ikruglov/home-automation/esp32-climarad-v2x/images/pcb-back.png

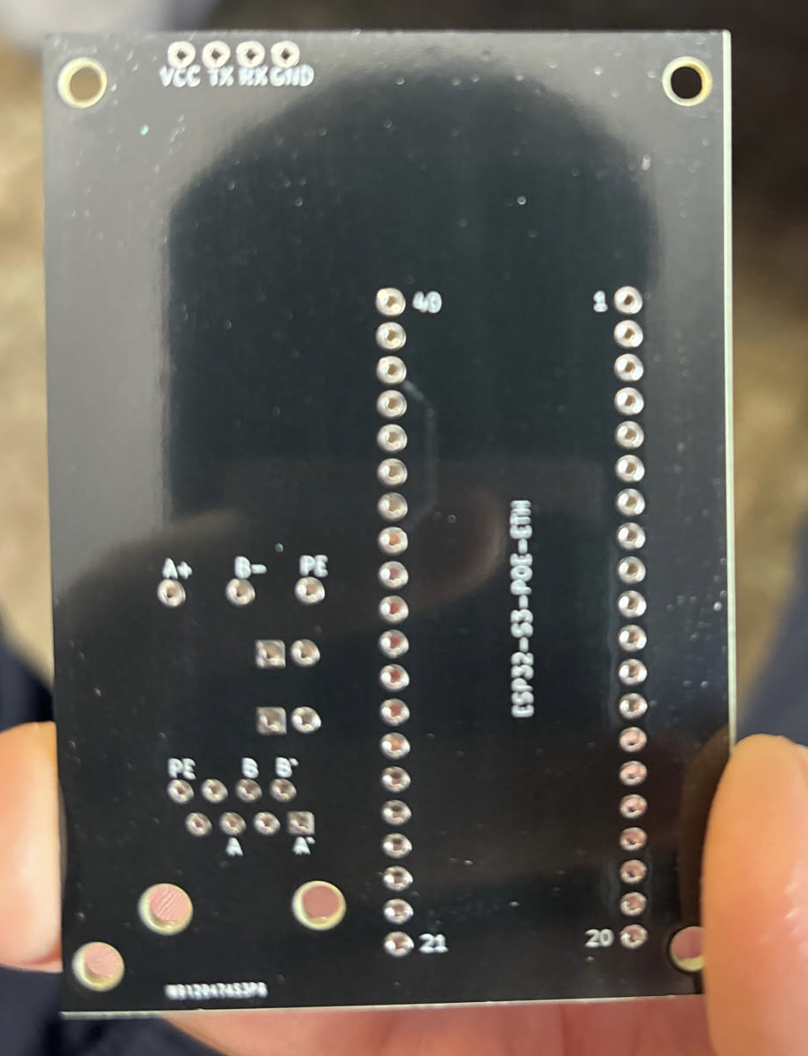
esp32-climarad-v2x/images/pcb-back.png
