ikruglov/home-automation/esp32-climarad-v2x/images/pcb-front.png

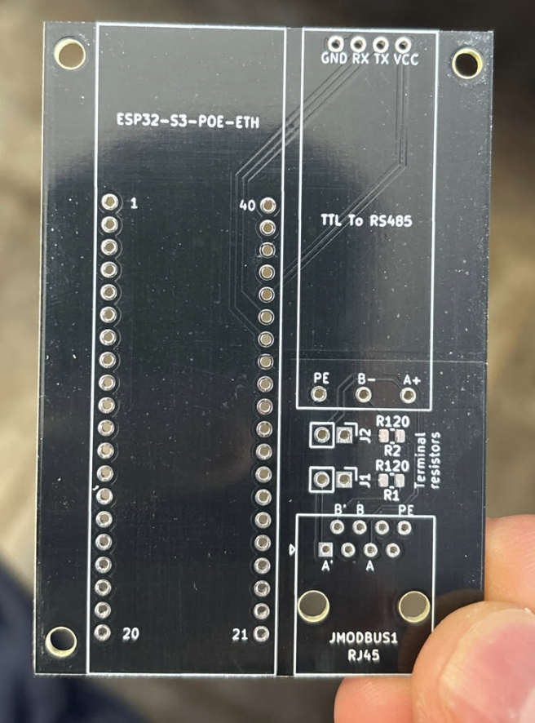
esp32-climarad-v2x/images/pcb-front.png
